omkarkarale/Circuit_Breakers/code/Medicine Dispenser/rtc.ino

#include <Wire.h>
#include <RTClib.h>

RTC_DS3231 rtc;

void setup() {
  Serial.begin(115200);

  Wire.begin(); // Uses Mega pins 20 and 21

  if (!rtc.begin()) {
    Serial.println("RTC not found");
    while (1);
  }

  // Uncomment once to set the time
  // rtc.adjust(DateTime(F(__DATE__), F(__TIME__)));
}

void loop() {
  DateTime now = rtc.now();

  Serial.print(now.day());
  Serial.print("/");
  Serial.print(now.month());
  Serial.print("/");
  Serial.print(now.year());

  Serial.print(" ");

  Serial.print(now.hour());
  Serial.print(":");
  Serial.print(now.minute());
  Serial.print(":");
  Serial.println(now.second());

  delay(1000);
}
