omkarkarale/Circuit_Breakers/Medicine_Dispenser/SOFTWARE/medlink-firmware_2.0/src_esp8266/Scheduler.h

#ifndef SCHEDULER_H
#define SCHEDULER_H

#include <Arduino.h>

class Scheduler {
public:
    static void begin();
    static void update();

    static void checkLowMedicine(int slot);
    static void resetLowWarned(int slot);
};

#endif // SCHEDULER_H
